bespoke-silicon-group/bsg_packaging/ucsd_bga_332/pinouts/bsg_three/tsmc_16/verilog/bsg_iopads_physical_only.v

// these are dedicated power pins and should not be
// instantiated as pins in the verilog
//

// `BSG_PHYSICAL_ONLY_PAD(PLL_VDD, PVDD_08_08_NT_DR_V)
// `BSG_PHYSICAL_ONLY_PAD(PLL_VSS, PVSS_08_08_NT_DR_V)
// `BSG_PHYSICAL_ONLY_PAD(PLL_V33, PDVDD_18_18_NT_DR_V)
// `BSG_PHYSICAL_ONLY_PAD(PLL_VZZ, PDVSS_18_18_NT_DR_V)

// Top
`BSG_PHYSICAL_ONLY_PAD(VDD_T_1, PVDD_08_08_NT_DR_V)
`BSG_PHYSICAL_ONLY_PAD(VDD_T_2, PVDD_08_08_NT_DR_V)
`BSG_PHYSICAL_ONLY_PAD(VDD_T_3, PVDD_08_08_NT_DR_V)
`BSG_PHYSICAL_ONLY_PAD(VDD_T_4, PVDD_08_08_NT_DR_V)
`BSG_PHYSICAL_ONLY_PAD(VDD_T_5, PVDD_08_08_NT_DR_V)
`BSG_PHYSICAL_ONLY_PAD(VDD_T_6, PVDD_08_08_NT_DR_V)
`BSG_PHYSICAL_ONLY_PAD(VDD_T_7, PVDD_08_08_NT_DR_V)
`BSG_PHYSICAL_ONLY_PAD(VDD_T_8, PVDD_08_08_NT_DR_V)
`BSG_PHYSICAL_ONLY_PAD(VDD_T_9, PVDD_08_08_NT_DR_V)
`BSG_PHYSICAL_ONLY_PAD(VDD_T_10, PVDD_08_08_NT_DR_V)

`BSG_PHYSICAL_ONLY_PAD(VSS_T_1, PVSS_08_08_NT_DR_V)
`BSG_PHYSICAL_ONLY_PAD(VSS_T_2, PVSS_08_08_NT_DR_V)
`BSG_PHYSICAL_ONLY_PAD(VSS_T_3, PVSS_08_08_NT_DR_V)
`BSG_PHYSICAL_ONLY_PAD(VSS_T_4, PVSS_08_08_NT_DR_V)
`BSG_PHYSICAL_ONLY_PAD(VSS_T_5, PVSS_08_08_NT_DR_V)
`BSG_PHYSICAL_ONLY_PAD(VSS_T_6, PVSS_08_08_NT_DR_V)
`BSG_PHYSICAL_ONLY_PAD(VSS_T_7, PVSS_08_08_NT_DR_V)
`BSG_PHYSICAL_ONLY_PAD(VSS_T_8, PVSS_08_08_NT_DR_V)
`BSG_PHYSICAL_ONLY_PAD(VSS_T_9, PVSS_08_08_NT_DR_V)
`BSG_PHYSICAL_ONLY_PAD(VSS_T_10, PVSS_08_08_NT_DR_V)

`BSG_PHYSICAL_ONLY_PAD(DVDD_T_1, PDVDD_18_18_NT_DR_V)
`BSG_PHYSICAL_ONLY_PAD(DVDD_T_2, PDVDD_18_18_NT_DR_V)
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
`BSG_PHYSICAL_ONLY_PAD(DVSS_R_4, PDVSS_18_18_NT_DR_H)
`BSG_PHYSICAL_ONLY_PAD(DVSS_R_5, PDVSS_18_18_NT_DR_H)
`BSG_PHYSICAL_ONLY_PAD(DVSS_R_6, PDVSS_18_18_NT_DR_H)
`BSG_PHYSICAL_ONLY_PAD(DVSS_R_7, PDVSS_18_18_NT_DR_H)
`BSG_PHYSICAL_ONLY_PAD(DVSS_R_8, PDVSS_18_18_NT_DR_H)

// Corner cells
// Instantiating the custom corner cell (and GPIO corner cell)
// during implementation to get around synthesis warnings of unresolved
// references.
// `BSG_PHYSICAL_ONLY_PAD(PCORNER_TOPRIGHT, PCORNER_STRETCHED_18_18_NT_DR)
// `BSG_PHYSICAL_ONLY_PAD(PCORNER_TOPLEFT, PCORNER_18_18_NT_DR)
// `BSG_PHYSICAL_ONLY_PAD(PCORNER_BOTTOMLEFT, PCORNER_18_18_NT_DR)
// `BSG_PHYSICAL_ONLY_PAD(PCORNER_BOTTOMRIGHT, PCORNER_18_18_NT_DR)
