bespoke-silicon-group/bsg_packaging/common/foundry/tsmc_180_250/verilog/bsg_iopad_macros.v

// **********************************************************************
// BEGIN TOP LEVEL I/O MACROS : BSG TWO (TSMC 180 nm)
//
// these macros define the PAD instantiations for general I/Os
// these macros will often be defined on a per-process basis,
// as the interfaces for the I/O macros change across generations.
//


`ifdef BSG_OUTPUTS_NEED_ENABLES
`define BSG_OUTPUT_ENABLE(name)  ,.OEN(name)
`define BSG_OUTPUT_ENABLE_WIRE(name) wire name;
`else
error BSG_OUTPUT_NEEDS_ENABLES not defined
`define BSG_OUTPUT_ENABLE(name)
`define BSG_OUTPUT_ENABLE_WIRE(name)
`endif


// **************************************************************************************************************
//

`define BSG_IO_TIEHI(name)                           \
  bsg_tiehi #(.width_p(1)) name``tiehi (.o(name));

`define BSG_IO_TIELO(name)                           \
  bsg_tielo #(.width_p(1)) name``tielo (.o(name));

`define BSG_IO_TIELO_VEC_ONE(name,item)                           \
  bsg_tielo #(.width_p(1)) name``_``_item``tielo (.o(name[item]));

`define BSG_IO_TIEHI_VEC_ONE(name,item)                           \
  bsg_tiehi #(.width_p(1)) name``_``_item``tiehi (.o(name[item]));

`define BSG_IO_TIEHI_VEC(name,width)             \
                                                 \
for (i=0; i < width;i=i+1)                       \
begin: tiehi_``name                              \
   bsg_tiehi #(.width_p(1)) hi (.o(name[i]));    \
end

`define BSG_IO_TIELO_VEC(name,width)             \
                                                 \
for (i=0; i < width;i=i+1)                       \
begin: tielo_``name                              \
   bsg_tielo #(.width_p(1)) lo (.o(name[i]));    \
end


`define BSG_IO_IN_DISABLE(name,padtype)                                       \
                                                                              \
  wire name``_oen_thi;                                                        \
  wire name``_tlo;                                                            \
                                                                              \
  `BSG_IO_TIEHI(name``_oen_thi)                                               \
  `BSG_IO_TIELO(name``_tlo)                                                   \
                                                                              \
                                                                              \
  padtype name``_i (.PAD(p_``name``_i), .OEN(name``_oen_thi), .I(name``_tlo));

// this is used to disable a differential input signal
// even though this is an input
// we employ an output pad and tri-state (OEN=1) the output
// we are trying to avoid the case of having an input
// pad with 1.2V LVDS voltage that creates short-circuit current in a 3.3V LVCMOS pad
// cell.

`define BSG_IO_IN_DIFF_DISABLE(name,padtype)  \
                                              \
  `BSG_IO_IN_DISABLE(name``_p,padtype)        \
  `BSG_IO_IN_DISABLE(name``_n,padtype)


// **************************************************************************************************************
// PDDDGZ foo_i (.PAD(p_foo_i), .C(foo_i_int));

`define BSG_IO_IN(name,padtype)                            \
                                                           \
   wire name``_i_int;                                      \
                                                           \
   padtype name``_i (.PAD(p_``name``_i), .C(name``_i_int));


// **************************************************************************************************************
// PDDDGZ sdi_A_sclk_ex_i (.PAD(p_sdi_sclk_ex_i[0]), .C(sdi_sclk_ex_i_int[0])); --> BSG_IO_IN_AO(sdi,sclk_ex,A,0)

`define BSG_IO_IN_A(pre,suffix,letter,index,padtype)                                                                \
                                                                                                                    \
   padtype pre``_``letter``_``suffix``_i (.PAD(p_``pre``_``suffix``_i[index]), .C(pre``_``suffix``_i_int[index]));



// **************************************************************************************************************
// PDDDGZ foo_0_i (.PAD(p_foo_i[0]), .C(foo_i_int[0]));

`define BSG_IO_IN_V(name,index,padtype) padtype name``_``index``_i (.PAD(p_``name``_i[index]), .C(name``_i_int[index]));



// **************************************************************************************************************
// PDT12DGZ foo_o (.PAD(p_foo_o), .OEN(foo_oen_int), .I(foo_o_int))

`define BSG_IO_OUT(name,padtype)                                                                \
                                                                                                \
   wire name``_o_int;                                                                           \
                                                                                                \
   `BSG_OUTPUT_ENABLE_WIRE(name``_oen_int)                                                       \
                                                                                                \
   padtype name``_o (.PAD(p_``name``_o) `BSG_OUTPUT_ENABLE(name``_oen_int) , .I(name``_o_int));



// **************************************************************************************************************
// PDT12DG foo_0_o (.PAD(p_foo_o[0]), .OEN(foo_oen_int[0]), .I(foo_o_int[0]))

`define BSG_IO_OUT_V(name,index,padtype)                                                                                           \
                                                                                                                                   \
     padtype name``_``index``_o (.PAD(p_``name``_o[index])  `BSG_OUTPUT_ENABLE(name``_oen_int[``index]), .I(name``_o_int[``index]));



// **************************************************************************************************************
// PDT12DGZ sdo_A_sclk_ex_o (.PAD(p_sdo_sclk_ex_o[0]), .OEN(sdo_sclk_ex_oen_int[0], .I(sdo_sclk_ex_o_int[0]))); --> BSG_OUT_AO(sdo,sclk_ex,A,0)

`define BSG_IO_OUT_A(pre,suffix,letter,num,padtype)                                                                                                            \
                                                                                                                                                               \
                                                                                                                                                               \
  padtype pre``_``letter``_``suffix``_o (.PAD(p_``pre``_``suffix``_o[num])  `BSG_OUTPUT_ENABLE(pre``_``suffix``_oen_int[num]), .I(pre``_``suffix``_o_int[num]));


// shared macros
`include "bsg_iopad_meta_macros.v"

//
//
// END TOP LEVEL I/O MACROS (180 nm)
// **********************************************************************
