bespoke-silicon-group/bsg_packaging/ucsd_bga_332/pinouts/bsg_three/tsmc_16/verilog/padmappings/one/bsg_padmapping.v

// pull in the macros that define I/Os for the chip
// this can also be swapped out for other technology files
// like verilog.

`define BSG_OUTPUTS_NEED_ENABLES

`define BSG_PAD_BIDIR_H PBIDIRN_18_18_FS_DR_H
`define BSG_PAD_BIDIR_V PBIDIRN_18_18_FS_DR_V
